jgilcas/A500-8MB-FastRAM/A500 FastRAM Bottom2.png

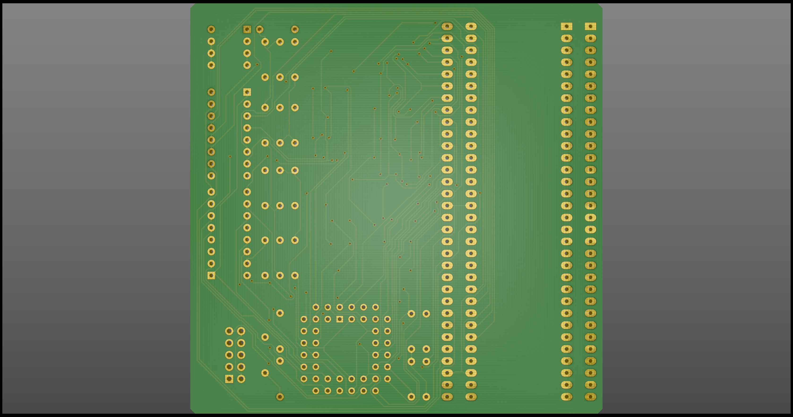
A500 FastRAM Bottom2.png
