jgilcas/A500-8MB-FastRAM/A500 FastRAM Top1b.png

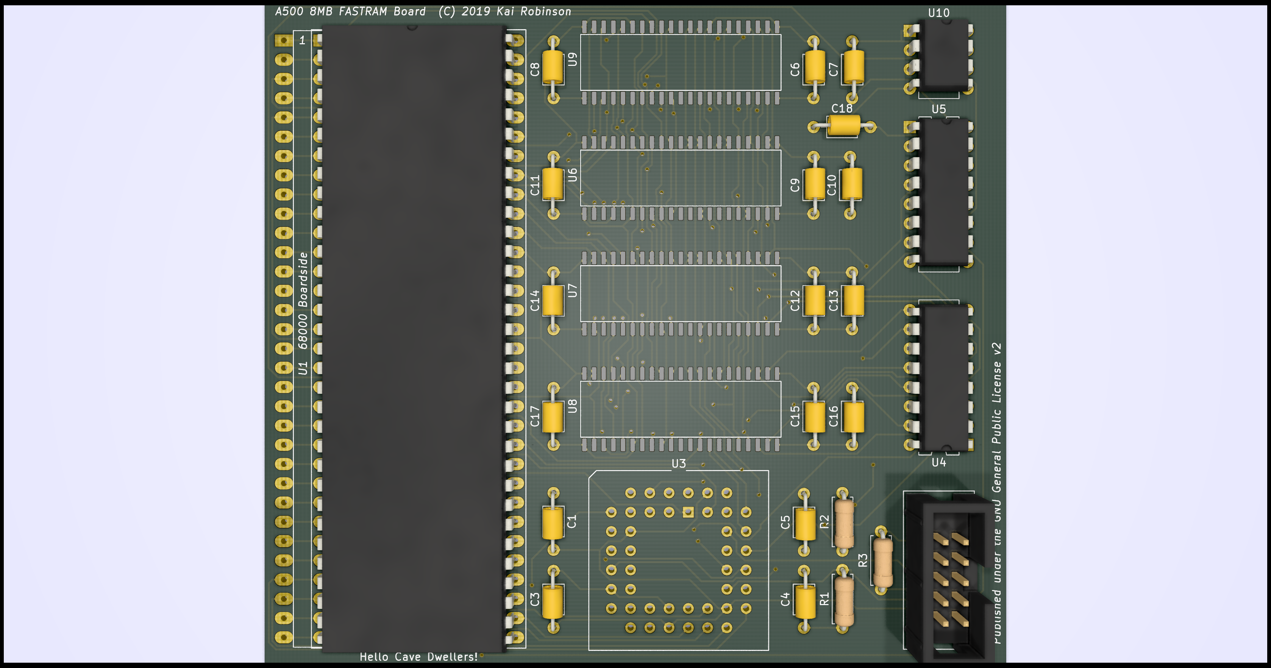
A500 FastRAM Top1b.png
