jgilcas/A500-8MB-FastRAM/code/A500 FastRAM Verilog.v

module a500_8mb( cpu_a21,cpu_a22,cpu_a23,
                 cpu_a1, cpu_a2, cpu_a3, cpu_a4, cpu_a5, cpu_a6,
                 cpu_a16,cpu_a17,cpu_a18,cpu_a19,cpu_a20,
                 cpu_d12,cpu_d13,cpu_d14,cpu_d15,
                 cpu_as,cpu_lds,cpu_uds,cpu_clk,
                 cpu_reset,
                 dram_ras0,dram_ras1,dram_ras2,dram_ras3, dram_lcas,dram_ucas,
                 dram_ma0,dram_ma1,
                 mux_switch
               );

	input cpu_a21,cpu_a22,cpu_a23; // cpu high addresses

	input cpu_a1, cpu_a2, cpu_a3, cpu_a4, cpu_a5, cpu_a6; // cpu low addresses for autoconfig
	input cpu_a16,cpu_a17,cpu_a18,cpu_a19,cpu_a20; // cpu high addresses for autoconfig

	inout cpu_d12,cpu_d13,cpu_d14,cpu_d15; // autoconfig data in-out
	reg   cpu_d12,cpu_d13,cpu_d14,cpu_d15;

	input cpu_as,cpu_lds,cpu_uds; // cpu bus control signals
	input cpu_clk; // cpu clock

	input cpu_reset; // cpu system reset

	output dram_ras0,dram_ras1,dram_ras2,dram_ras3;
	reg    dram_ras0,dram_ras1,dram_ras2,dram_ras3; // /RAS dram signals

	output dram_lcas,dram_ucas;
	reg    dram_lcas,dram_ucas; // /CAS dram signals

	output dram_ma0,dram_ma1;
	reg    dram_ma0,dram_ma1; // DRAM MAx addresses

	output mux_switch;
	reg    mux_switch; // external MUX switching


	reg  [3:0] datout; // data out

	wire [7:0] high_addr;
	wire [5:0] low_addr;

	reg which_ras[0:3]; // which /RAS signal to activate (based on a21-a23)
	reg mem_selected;

	reg rfsh_ras,rfsh_cas; // refresh /RAS, /CAS generators

	reg access_ras,access_cas; // normal access /RAS, /CAS generators

	reg read_cycle; // if current cycle is read cycle
	reg write_cycle;
	reg autoconf_on;
	reg cpu_as_z; // cpu /AS with 1 clock latency

	reg [1:0] rfsh_select; // for cycling refresh over every of four chips


	assign high_addr = {cpu_a23,cpu_a22,cpu_a21,cpu_a20,cpu_a19,cpu_a18,cpu_a17,cpu_a16};
	assign low_addr  = {cpu_a6,cpu_a5,cpu_a4,cpu_a3,cpu_a2,cpu_a1};

	// chip selector decoder
	always @*
	begin
		casex( high_addr )
		8'b001xxxxx: // $200000-$3fffff
		begin
			{which_ras[0],which_ras[1],which_ras[2],which_ras[3]} <= 4'b1000; // /RAS0
			mem_selected <= 1'b1;
		end

		8'b010xxxxx: // $400000-$5fffff
		begin
			{which_ras[0],which_ras[1],which_ras[2],which_ras[3]} <= 4'b0100; // /RAS1
			mem_selected <= 1'b1;
		end

		// remove this two CASE sections below for 4Mb only decoding (do not remove "default:"!)
		8'b011xxxxx: // $600000-$7fffff
		begin
			{which_ras[0],which_ras[1],which_ras[2],which_ras[3]} <= 4'b0010; // /RAS2
			mem_selected <= 1'b1;
		end

		8'b100xxxxx: // $800000-$9fffff
		begin
			{which_ras[0],which_ras[1],which_ras[2],which_ras[3]} <= 4'b0001; // /RAS3
			mem_selected <= 1'b1;
		end

		default:
		begin
			{which_ras[0],which_ras[1],which_ras[2],which_ras[3]} <= 4'b0000; // nothing
			mem_selected <= 1'b0;
		end

		endcase
	end


	// normal cycle generator
	always @(posedge cpu_clk,posedge cpu_as)
	begin
		if( cpu_as==1 )
		begin // /AS=1
			access_ras <= 0;
			access_cas <= 0;
		end
		else
		begin // /AS=0, positive clock
			access_ras <= 1;
			access_cas <= access_ras; // one clock later
		end
	end

	// MUX switcher generator
	always @(negedge cpu_clk,negedge access_ras)
	begin
		if( access_ras==0 )
		begin // reset on no access_ras
			mux_switch <= 0;
		end
		else
		begin // set to 1 on negedge after beginning of access_ras
			mux_switch <= 1;
		end
	end




	// refresh cycle generator
	always @(negedge cpu_clk)
	begin
		if( cpu_as==1 ) // /AS negated
		begin
			rfsh_cas <= ~rfsh_cas;
		end
		else // /AS asserted
		begin
			rfsh_cas <= 0;
		end

		if( (rfsh_cas == 1'b0) && (cpu_as==1) )
		begin
			rfsh_select <= rfsh_select + 2'b01;
		end
	end

	always @*
	begin
		rfsh_ras <= rfsh_cas & cpu_clk;
	end



	// output signals generator
	always @*
	begin
		dram_ras0 <= ~( ( which_ras[0] & access_ras ) | ((rfsh_select==2'b00)?rfsh_ras:1'b0) );
		dram_ras1 <= ~( ( which_ras[1] & access_ras ) | ((rfsh_select==2'b01)?rfsh_ras:1'b0) );
		dram_ras2 <= ~( ( which_ras[2] & access_ras ) | ((rfsh_select==2'b10)?rfsh_ras:1'b0) );
		dram_ras3 <= ~( ( which_ras[3] & access_ras ) | ((rfsh_select==2'b11)?rfsh_ras:1'b0) );

		dram_lcas <= ~( ( ~cpu_lds & access_cas & mem_selected ) | rfsh_cas );
		dram_ucas <= ~( ( ~cpu_uds & access_cas & mem_selected ) | rfsh_cas );
	end





	// DRAM MAx multiplexor
	always @*
	begin
		if( mux_switch==0 )
			{ dram_ma0,dram_ma1 } <= { cpu_a1,cpu_a2 };
		else // mux_switch==1
			{ dram_ma0,dram_ma1 } <= { cpu_a20,cpu_a19 };
	end


	// make clocked cpu_as_z
	always @(posedge cpu_clk)
	begin
		cpu_as_z <= cpu_as;
	end

	// detect if current cycle is read or write cycle
	always @(posedge cpu_clk, posedge cpu_as)
	begin
		if( cpu_as==1 ) // async reset on end of /AS strobe
		begin
			read_cycle  <= 0; // end of cycles
			write_cycle <= 0;
		end
		else // sync beginning of cycle
		begin
			if( cpu_as==0 && cpu_as_z==1 ) // beginning of /AS strobe
			begin
				if( (cpu_lds&cpu_uds)==0 )
					read_cycle <= 1;
				else
					write_cycle <= 1;
			end
		end
	end

	// autoconfig data forming
	always @*
	begin
		case( low_addr )
		6'b000000: // $00
			datout <= 4'b1110;
		6'b000001: // $02
			datout <= 4'b0000; // 0111 for 4mb, 0000 for 8mb

		6'b000010: // $04
			datout <= 4'hE;
		6'b000011: // $06
			datout <= 4'hE;

		6'b000100: // $08
			datout <= 4'h3;
		6'b000101: // $0a
			datout <= 4'hF;

		6'b001000: // $10
			datout <= 4'hE;
		6'b001001: // $12
			datout <= 4'hE;

		6'b001010: // $14
			datout <= 4'hE;
		6'b001011: // $16
			datout <= 4'hE;

		6'b100000: // $40
			datout <= 4'b0000;
		6'b100001: // $42
			datout <= 4'b0000;

		default:
			datout <= 4'b1111;
		endcase
	end

	// out autoconfig data
	always @*
	begin
		if( read_cycle==1 && high_addr==8'hE8 && autoconf_on==1 )
			{cpu_d15,cpu_d14,cpu_d13,cpu_d12} <= datout;
		else
			{cpu_d15,cpu_d14,cpu_d13,cpu_d12} <= 4'bZZZZ;
	end

	// autoconfig cycle on/off
	always @(posedge write_cycle,negedge cpu_reset)
	begin
		if( cpu_reset==0 ) // reset - begin autoconf
			autoconf_on <= 1;
		else
		begin
			if( high_addr==8'hE8 && low_addr[5:2]==4'b1001 ) // $E80048..$E8004E
				autoconf_on <= 0;
		end
	end



endmodule
